kcynn/Triceratops_Robot/Triceratop_Mechanic/Part5.SLDPRT

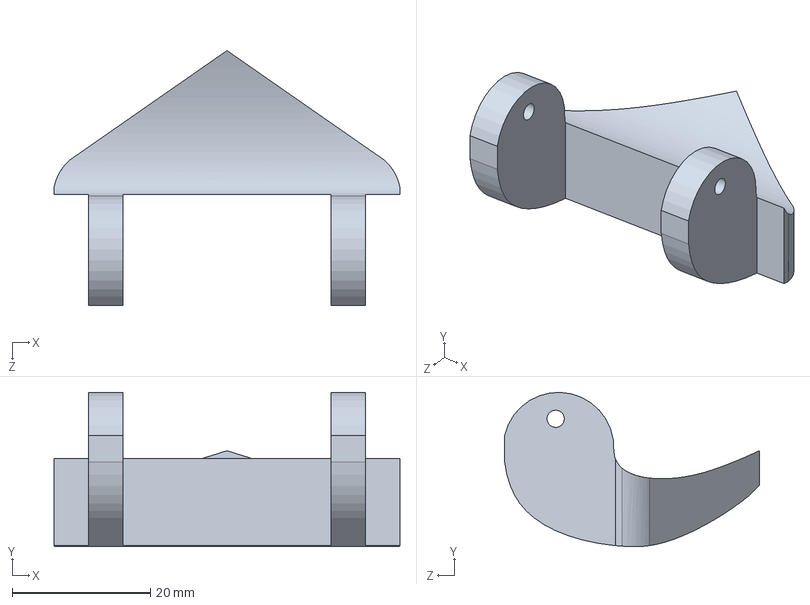
[picture p28: CAD file, 2024-05-20]
Triceratop_Mechanic/Part5.SLDPRT
50.0 x 22.3 x 36.8 mm
