kcynn/Triceratops_Robot/Triceratop_Mechanic/f3.SLDPRT

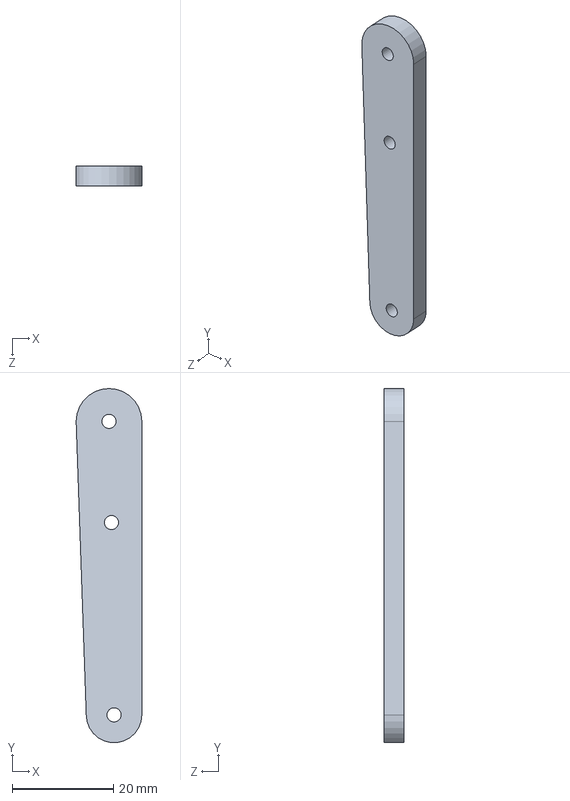
[picture p29: CAD file, 2024-05-20]
Triceratop_Mechanic/f3.SLDPRT
13.0 x 70.0 x 4.00 mm
