kcynn/Triceratops_Robot/Triceratop_Mechanic/Part2.SLDPRT

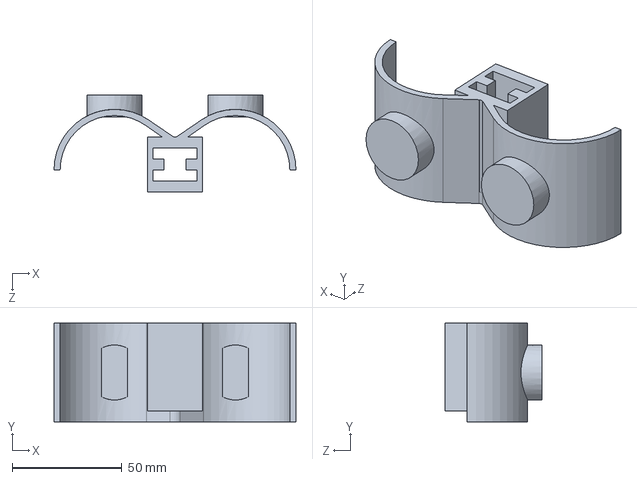
[picture p30: CAD file, 2024-05-20]
Triceratop_Mechanic/Part2.SLDPRT
110.0 x 45.0 x 44.0 mm
