kcynn/Triceratops_Robot/Triceratop_Mechanic/Part_F1.SLDPRT

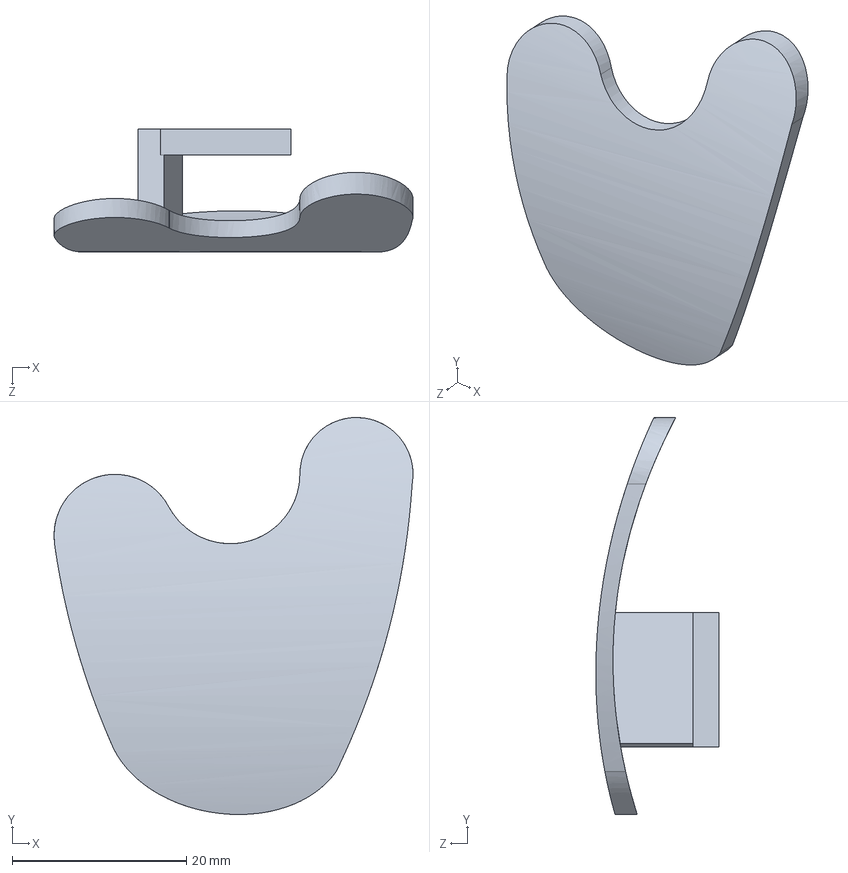
[picture p31: CAD file, 2024-05-20]
Triceratop_Mechanic/Part_F1.SLDPRT
41.2 x 45.6 x 14.2 mm
