kcynn/Triceratops_Robot/Triceratop_Mechanic/Part12.SLDPRT

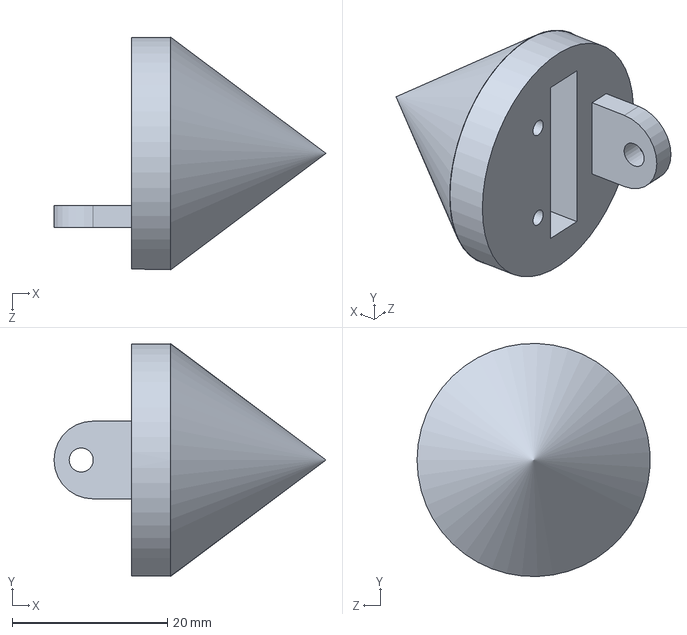
[picture p32: CAD file, 2024-05-20]
Triceratop_Mechanic/Part12.SLDPRT
35.0 x 30.0 x 30.0 mm
