kcynn/Triceratops_Robot/Triceratop_Mechanic/b2.SLDPRT

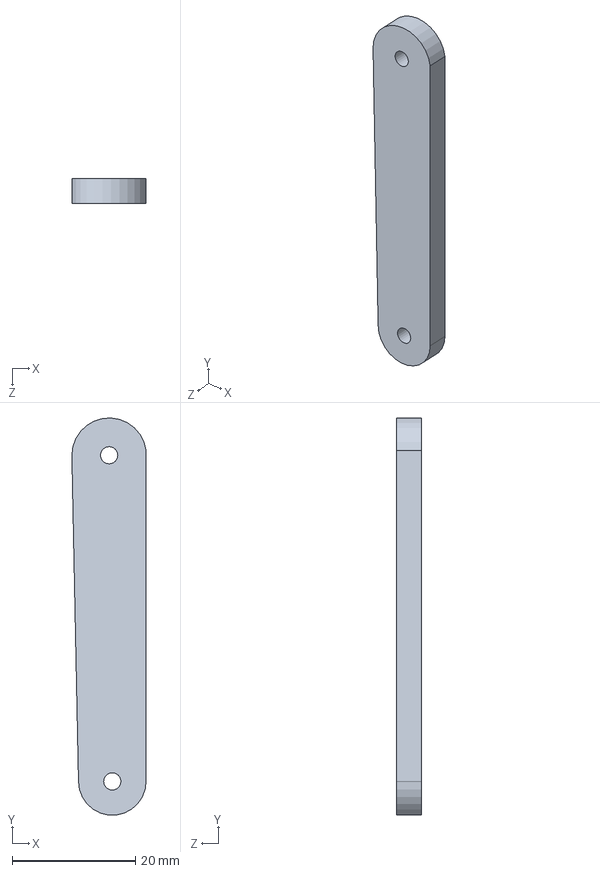
[picture p33: CAD file, 2024-05-20]
Triceratop_Mechanic/b2.SLDPRT
12.1 x 64.5 x 4.00 mm
