kcynn/Triceratops_Robot/Triceratop_Mechanic/f2.SLDPRT

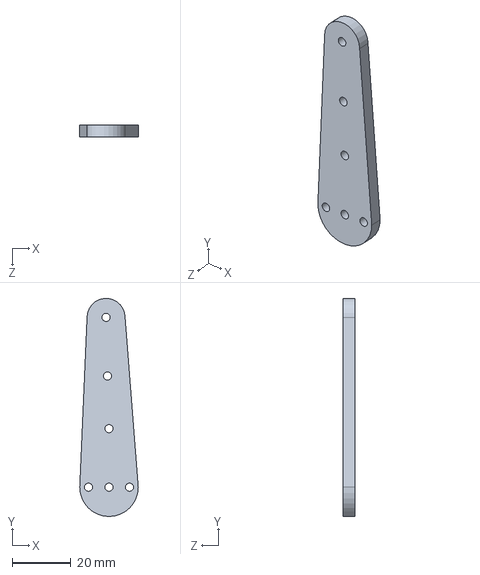
[picture p34: CAD file, 2024-05-20]
Triceratop_Mechanic/f2.SLDPRT
20.0 x 74.5 x 4.00 mm
