kcynn/Triceratops_Robot/Triceratop_Mechanic/Part6.SLDPRT

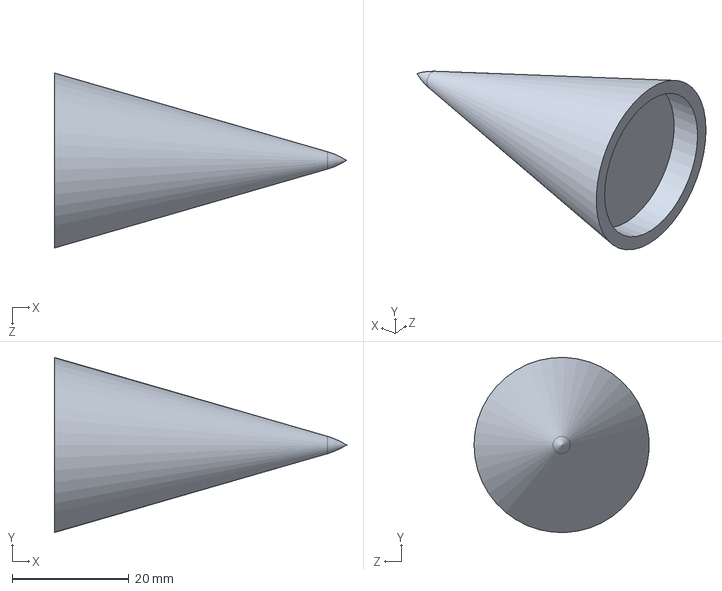
[picture p35: CAD file, 2024-05-20]
Triceratop_Mechanic/Part6.SLDPRT
50.0 x 30.0 x 30.0 mm
