kcynn/Triceratops_Robot/Triceratop_Mechanic/Part9.SLDPRT

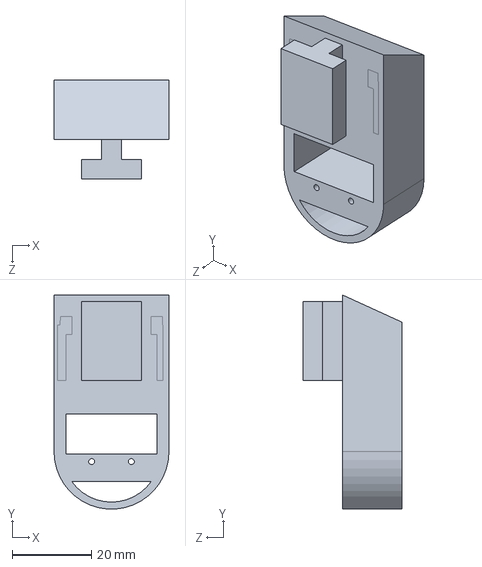
[picture p36: CAD file, 2024-05-20]
Triceratop_Mechanic/Part9.SLDPRT
28.9 x 53.9 x 25.0 mm
