kcynn/Triceratops_Robot/Triceratop_Mechanic/f1.SLDPRT

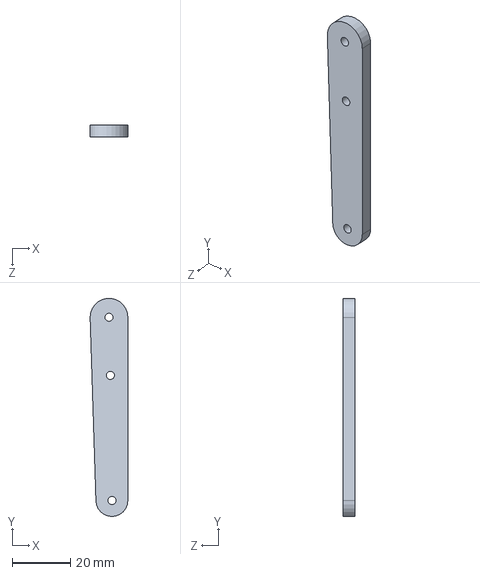
[picture p37: CAD file, 2024-05-20]
Triceratop_Mechanic/f1.SLDPRT
13.0 x 75.0 x 4.00 mm
