kcynn/Triceratops_Robot/Triceratop_Mechanic/Part15.SLDPRT

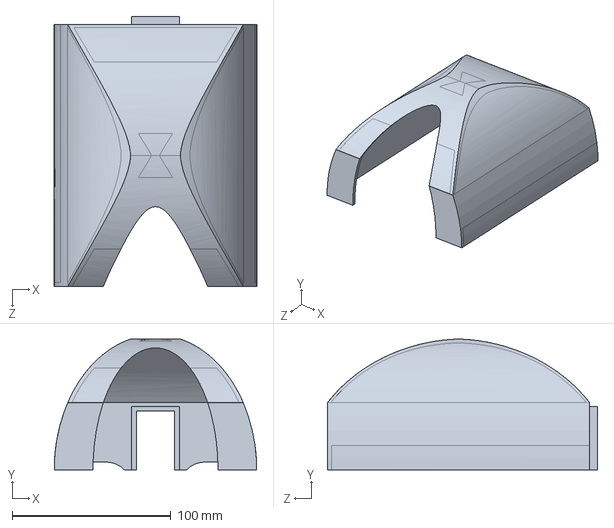
[picture p38: CAD file, 2024-05-20]
Triceratop_Mechanic/Part15.SLDPRT
127.5 x 82.4 x 170.0 mm
