kcynn/Triceratops_Robot/Triceratop_Mechanic/Part2-15.SLDPRT

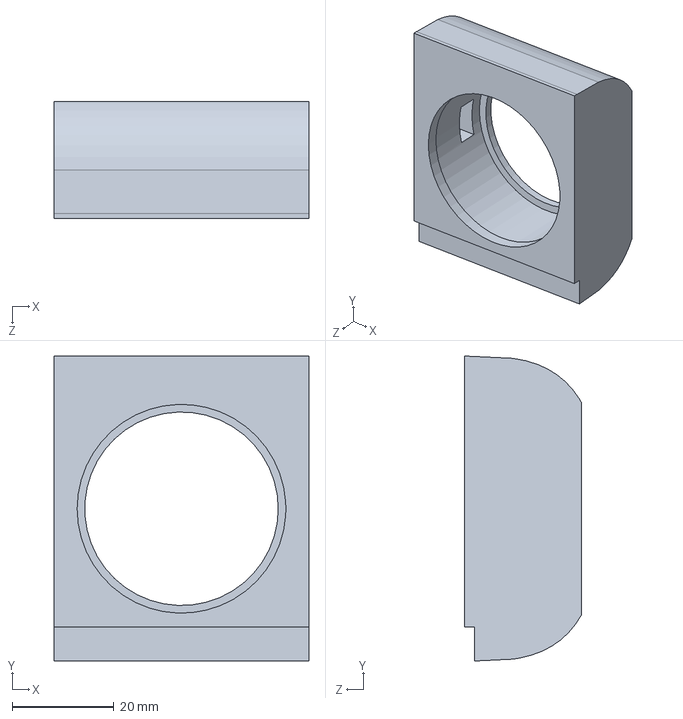
[picture p39: CAD file, 2024-05-20]
Triceratop_Mechanic/Part2-15.SLDPRT
50.0 x 59.9 x 23.0 mm
