kcynn/Triceratops_Robot/Triceratop_Mechanic/Part13-14.SLDPRT

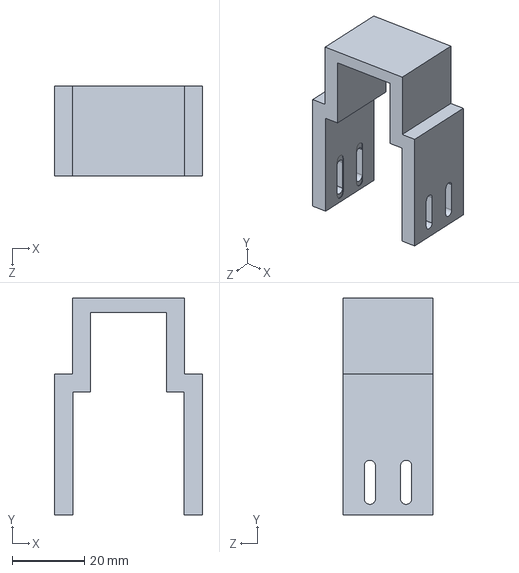
[picture p40: CAD file, 2024-05-20]
Triceratop_Mechanic/Part13-14.SLDPRT
41.0 x 60.0 x 25.0 mm
