kcynn/Triceratops_Robot/Triceratop_Mechanic/b1.SLDPRT

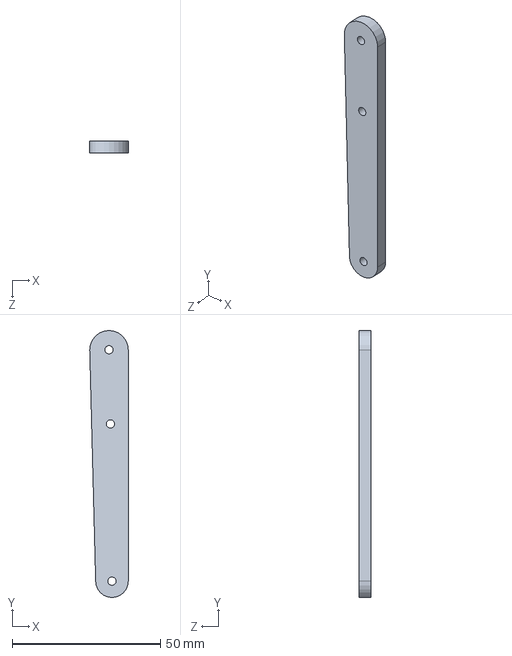
[picture p41: CAD file, 2024-05-20]
Triceratop_Mechanic/b1.SLDPRT
13.0 x 90.0 x 4.00 mm
