kcynn/Triceratops_Robot/Triceratop_Mechanic/Part13.SLDPRT

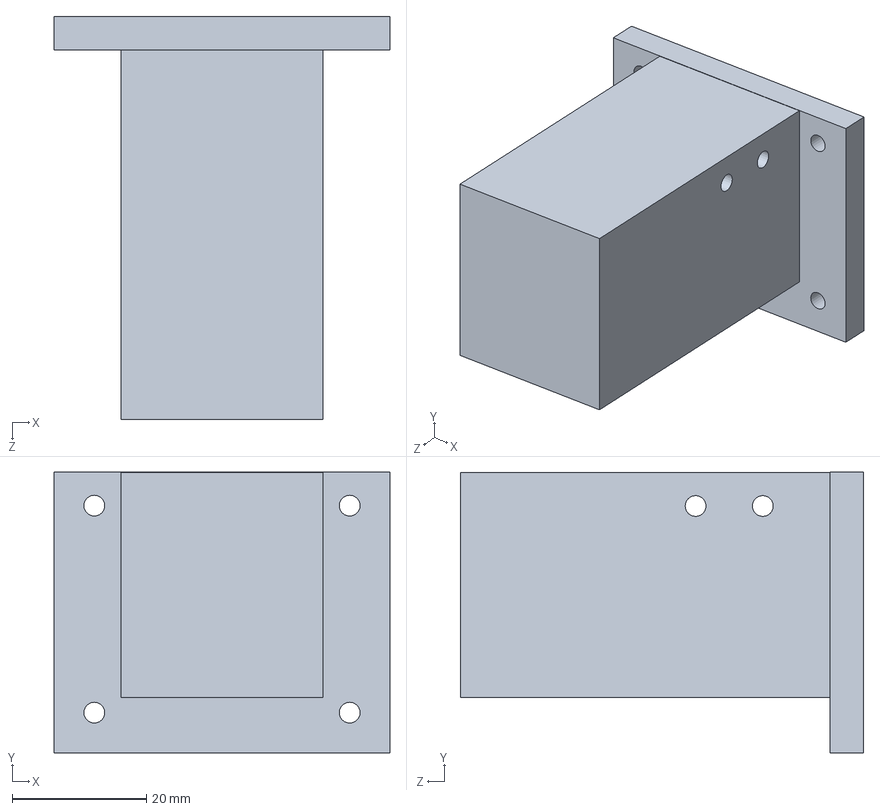
[picture p42: CAD file, 2024-05-20]
Triceratop_Mechanic/Part13.SLDPRT
50.0 x 41.8 x 60.0 mm
