kcynn/Triceratops_Robot/Triceratop_Mechanic/Part11.SLDPRT

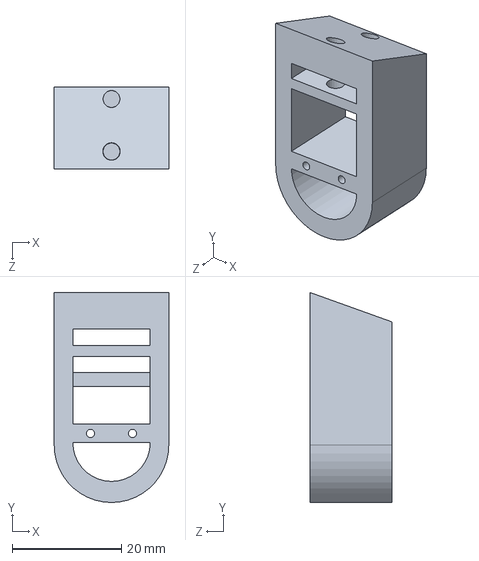
[picture p43: CAD file, 2024-05-20]
Triceratop_Mechanic/Part11.SLDPRT
21.0 x 38.4 x 15.0 mm
