kcynn/Triceratops_Robot/Triceratop_Mechanic/Part_F2.SLDPRT

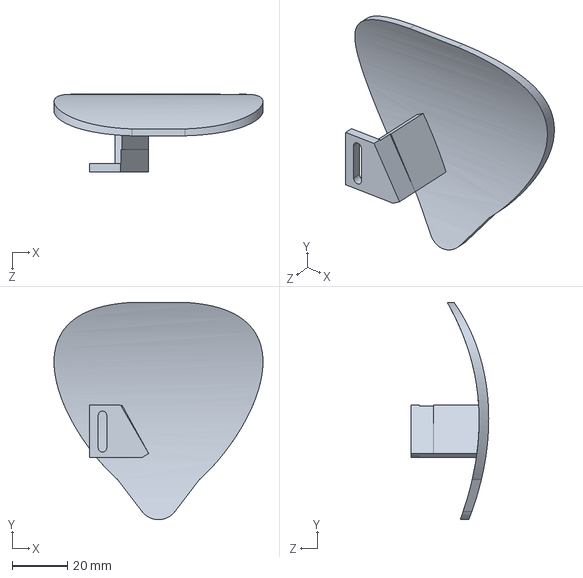
[picture p44: CAD file, 2024-05-20]
Triceratop_Mechanic/Part_F2.SLDPRT
75.6 x 78.6 x 28.0 mm
